pseudoincorrect/Dehydration/dehydration_emb_sys/dehydration/Node_server/src/nodeHal/nodeHal_saadc.c

#include "nodeHal_saadc.h"

static nrf_saadc_value_t     m_buffer_pool[2][SAMPLES_IN_BUFFER];
static nrf_ppi_channel_t     m_ppi_channel;
static const nrf_drv_timer_t m_timer = NRF_DRV_TIMER_INSTANCE(4);

void nodeHal_saadc_sampling_event_enable(void)
{
    ret_code_t err_code = nrf_drv_ppi_channel_enable(m_ppi_channel);

    ERROR_CHECK(err_code);
}

void nodeHal_saadc_sampling_event_init(void)
{
    ret_code_t err_code;

    err_code = nrf_drv_ppi_init();
    APP_ERROR_CHECK(err_code);

    nrf_drv_timer_config_t timer_cfg = NRF_DRV_TIMER_DEFAULT_CONFIG;
    timer_cfg.bit_width = NRF_TIMER_BIT_WIDTH_32;
    err_code = nrf_drv_timer_init(&m_timer, &timer_cfg, timer_handler);
    APP_ERROR_CHECK(err_code);

    // setup m_timer for compare event
    uint32_t ticks = nrf_drv_timer_ms_to_ticks(&m_timer, 1000);
    nrf_drv_timer_extended_compare(&m_timer,
                                   NRF_TIMER_CC_CHANNEL0,
                                   ticks,
                                   NRF_TIMER_SHORT_COMPARE0_CLEAR_MASK,
                                   false);
    nrf_drv_timer_enable(&m_timer);

    uint32_t timer_compare_event_addr =
        nrf_drv_timer_compare_event_address_get(
                                            &m_timer,NRF_TIMER_CC_CHANNEL0);
    uint32_t saadc_sample_task_addr   = nrf_drv_saadc_sample_task_get();

    // setup timer compare event is triggering sample task in SAADC
    err_code = nrf_drv_ppi_channel_alloc(&m_ppi_channel);
    APP_ERROR_CHECK(err_code);

    err_code = nrf_drv_ppi_channel_assign(m_ppi_channel,
                                          timer_compare_event_addr,
                                          saadc_sample_task_addr);
    APP_ERROR_CHECK(err_code);
}


void nodeHal_saadc_init(void* saadc_callback)
{
    ret_code_t err_code;
    nrf_saadc_channel_config_t channel_config =
        NRF_DRV_SAADC_DEFAULT_CHANNEL_CONFIG_SE(TEMP_SKIN_AIN);

    err_code = nrf_drv_saadc_init(NULL, saadc_callback);
    ERROR_CHECK(err_code);

    err_code = nrf_drv_saadc_channel_init(0, &channel_config);
    ERROR_CHECK(err_code);

    // err_code = nrf_drv_saadc_buffer_convert(
    //                                     m_buffer_pool[0], SAMPLES_IN_BUFFER);
    // ERROR_CHECK(err_code);

    // err_code = nrf_drv_saadc_buffer_convert(
    //                                     m_buffer_pool[1], SAMPLES_IN_BUFFER);
    ERROR_CHECK(err_code);

    // nodeHal_saadc_sampling_event_init();
    // nodeHal_saadc_sampling_event_enable();
}


void nodeHal_saadc_init_simple(void)
{
   // Configure SAADC singled-ended channel, Internal reference (0.6V) and 1/6 gain.
  NRF_SAADC->CH[0].CONFIG = (SAADC_CH_CONFIG_GAIN_Gain1_6    << SAADC_CH_CONFIG_GAIN_Pos) |
                            (SAADC_CH_CONFIG_MODE_SE         << SAADC_CH_CONFIG_MODE_Pos) |
                            (SAADC_CH_CONFIG_REFSEL_Internal << SAADC_CH_CONFIG_REFSEL_Pos) |
                            (SAADC_CH_CONFIG_RESN_Bypass     << SAADC_CH_CONFIG_RESN_Pos) |
                            (SAADC_CH_CONFIG_RESP_Bypass     << SAADC_CH_CONFIG_RESP_Pos) |
                            (SAADC_CH_CONFIG_TACQ_3us        << SAADC_CH_CONFIG_TACQ_Pos);

  // Configure the SAADC channel with VDD as positive input, no negative input(single ended).
  // NRF_SAADC->CH[0].PSELP = NRF_SAADC_INPUT_AIN5;
  NRF_SAADC->CH[0].PSELN = SAADC_CH_PSELN_PSELN_NC << SAADC_CH_PSELN_PSELN_Pos;

  // Configure the SAADC resolution.
  NRF_SAADC->RESOLUTION = SAADC_RESOLUTION_VAL_14bit << SAADC_RESOLUTION_VAL_Pos;

  // Configure result to be put in RAM at the location of "result" variable.
  NRF_SAADC->RESULT.MAXCNT = 1;
  // NRF_SAADC->RESULT.PTR = (uint32_t*) result;

  // No automatic sampling, will trigger with TASKS_SAMPLE.
  NRF_SAADC->SAMPLERATE = SAADC_SAMPLERATE_MODE_Task << SAADC_SAMPLERATE_MODE_Pos;

  // Enable SAADC (would capture analog pins if they were used in CH[0].PSELP)
  NRF_SAADC->ENABLE = SAADC_ENABLE_ENABLE_Enabled << SAADC_ENABLE_ENABLE_Pos;

  // Calibrate the SAADC (only needs to be done once in a while)
  NRF_SAADC->TASKS_CALIBRATEOFFSET = 1;
  while (NRF_SAADC->EVENTS_CALIBRATEDONE == 0);
  NRF_SAADC->EVENTS_CALIBRATEDONE = 0;
  while (NRF_SAADC->STATUS == (SAADC_STATUS_STATUS_Busy <<SAADC_STATUS_STATUS_Pos));


}

void nodeHal_saadc_sample_simple(nrf_saadc_input_t saadc_pin, int16_t* result_ptr)
{
        NRF_SAADC->CH[0].PSELP = saadc_pin;
        NRF_SAADC->RESULT.PTR = (uint32_t*) result_ptr;

        // Start the SAADC and wait for the started event.
        NRF_SAADC->TASKS_START = 1;
        while (NRF_SAADC->EVENTS_STARTED == 0);
        NRF_SAADC->EVENTS_STARTED = 0;
        // Do a SAADC sample, will put the result in the configured RAM buffer.
        NRF_SAADC->TASKS_SAMPLE = 1;
        while (NRF_SAADC->EVENTS_END == 0);
        NRF_SAADC->EVENTS_END = 0;
        // Stop the SAADC, since it's not used anymore.
        NRF_SAADC->TASKS_STOP = 1;
        while (NRF_SAADC->EVENTS_STOPPED == 0);
        NRF_SAADC->EVENTS_STOPPED = 0;
}

void timer_handler(nrf_timer_event_t event_type, void * p_context)
{
    ;
}
