pseudoincorrect/Dehydration/dehydration_emb_sys/dehydration/Node_server/src/nodeHal/nodeHal_oneWire.h

#ifndef DHT22_H_
#define DHT22_H_


#include <stdint.h>
#include "nodeHal_gpio.h"
#include "nrf_delay.h"
#include "nrf_timer.h"
#include "SEGGER_RTT.h"

/* Port and pin with DHT22 sensor*/

/* DHT22_GetReadings response codes */
#define DHT22_RCV_OK            0 // Return with no error
#define DHT22_RCV_NO_RESPONSE   1 // No response from sensor
#define DHT22_RCV_BAD_ACK1      2 // Bad first half length of ACK impulse
#define DHT22_RCV_BAD_ACK2      3 // Bad second half length of ACK impulse
#define DHT22_RCV_TIMEOUT       4 // Timeout while receiving bits
#define DHT22_BAD_DATA          5 // Bad data received


typedef struct dht22_data
{
  volatile uint8_t rcv_response;
  volatile float temperature;
  volatile float humidity;
  uint8_t parity;
  uint8_t parity_rcv;
  uint8_t hMSB;
  uint8_t hLSB;
  uint8_t tMSB;
  uint8_t tLSB;
  uint8_t bits[40];
} dht22_data;


void DHT22_Init (void);
bool DHT22_Read (dht22_data *out);
// void DHT22_Read (void);


#endif /* DHT22_H_ */
