pseudoincorrect/Dehydration/dehydration_GUI/Employee_overview_ui.py

# -*- coding: utf-8 -*-

# Form implementation generated from reading ui file '.\Employee_overview.ui'
#
# Created by: PyQt5 UI code generator 5.10.1
#
# WARNING! All changes made in this file will be lost!
